MrKohESP/GAmP/IMG_4971.jpg

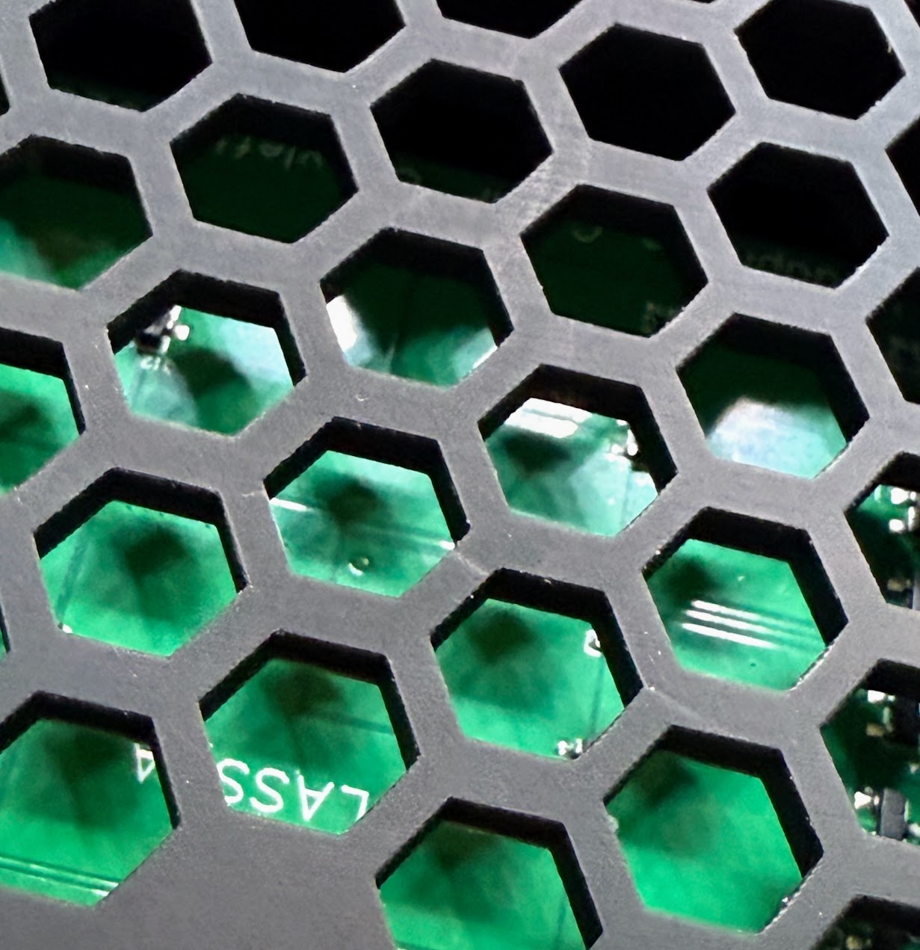
IMG_4971.jpg
